Engineering-House/Project-Synthia/synthia/Symbol-and-Footprints/3D_models/SJ3-35083C-TR.step

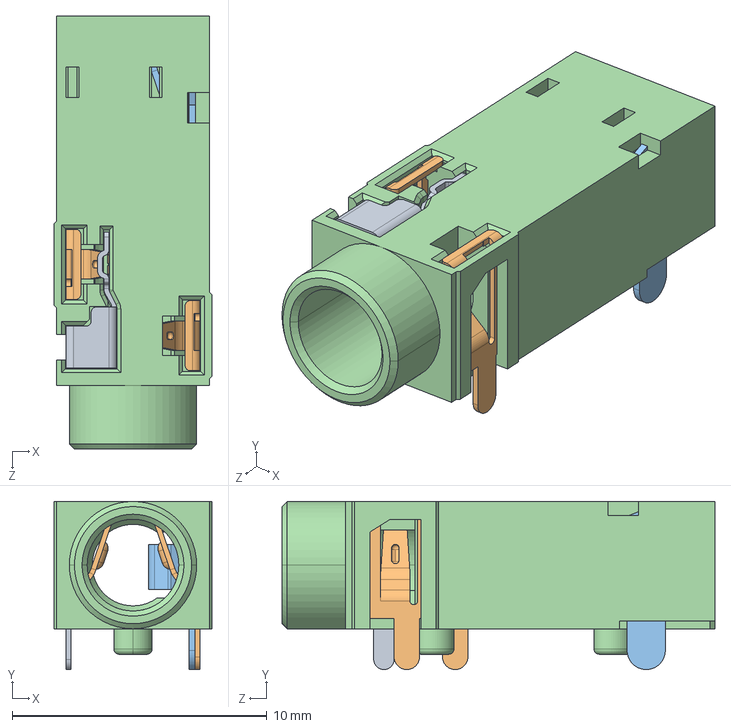
[picture p15: CAD file, 2026-04-25]
synthia/Symbol-and-Footprints/3D_models/SJ3-35083C-TR.step
6.20 x 6.60 x 17.0 mm
