Engineering-House/Project-Synthia/synthia/Symbol-and-Footprints/3D_models/PJ-007.step

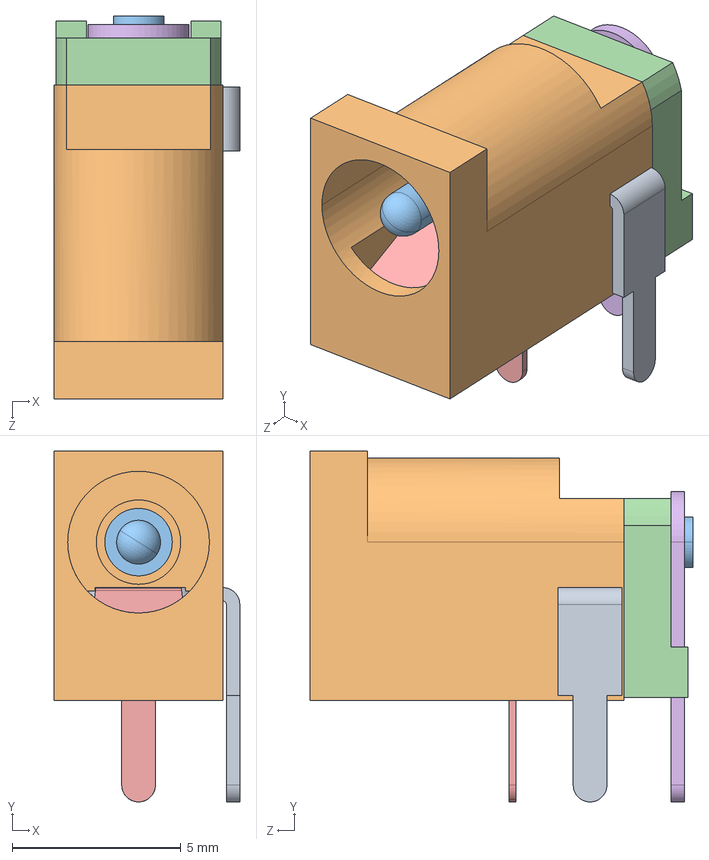
[picture p16: CAD file, 2026-04-25]
synthia/Symbol-and-Footprints/3D_models/PJ-007.step
5.50 x 10.4 x 11.4 mm
