Engineering-House/Project-Synthia/synthia/Symbol-and-Footprints/3D_models/TLV272IP.step

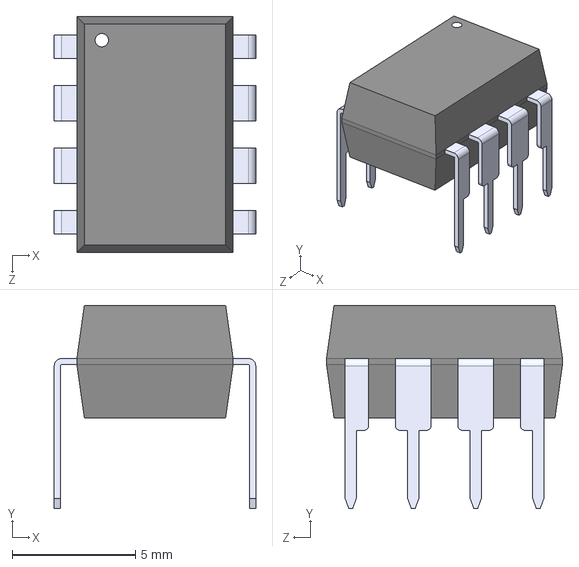
[picture p17: CAD file, 2026-03-29]
synthia/Symbol-and-Footprints/3D_models/TLV272IP.step
8.19 x 8.26 x 9.59 mm
