Engineering-House/Project-Synthia/synthia/Symbol-and-Footprints/3D_models/LD1117V33.step

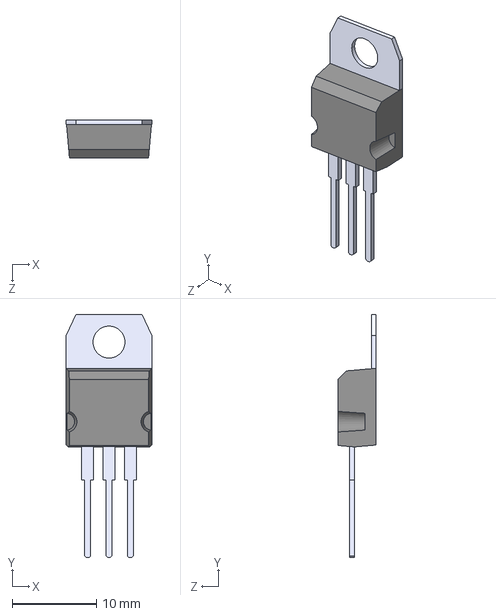
[picture p18: CAD file, 2026-03-26]
synthia/Symbol-and-Footprints/3D_models/LD1117V33.step
10.2 x 28.9 x 4.50 mm
