Engineering-House/Project-Synthia/synthia/Symbol-and-Footprints/3D_models/TL1105BF160Q.step

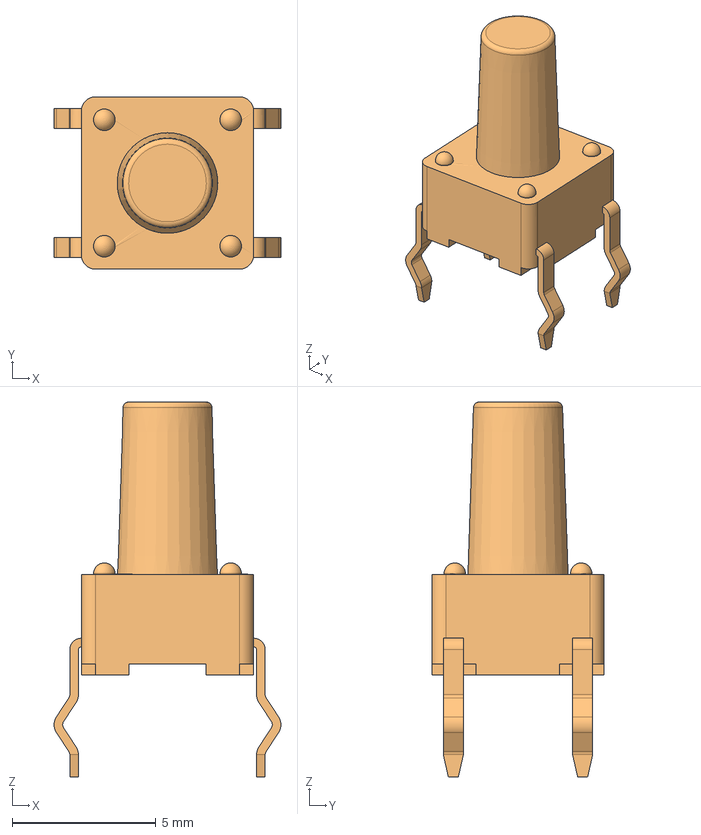
[picture p19: CAD file, 2026-03-26]
synthia/Symbol-and-Footprints/3D_models/TL1105BF160Q.step
7.89 x 6.00 x 13.1 mm
